dijkstrw/5x5/debug.c

/*
 * Debugging routines that help determine the nature of hard faults
 *
 * When linked in will override libopencm3's default hardfault handler.
 *
 * Original by Erich Styger via
 * http://mcuoneclipse.com/2012/11/24/debugging-hard-faults-on-arm-cortex-m/
 */

#include <libopencm3/cm3/scb.h>

void hardfault_discovery(struct scb_exception_stack_frame *frame);
void hardfault_discovery(struct scb_exception_stack_frame *frame)
{
    volatile uint32_t _CFSR;
    volatile uint32_t _HFSR;
    volatile uint32_t _DFSR;
    volatile uint32_t _AFSR;
    volatile uint32_t _BFAR;
    volatile uint32_t _MMAR;

    (void)(frame);
    /*
     * - Configurable Fault Status Register, MMSR, BFSR and UFSR
     * - Hard Fault Status Register
     * - Debug Fault Status Register
     * - Auxiliary Fault Status Register
     */
    _CFSR = SCB_CFSR;
    _HFSR = SCB_HFSR;
    _DFSR = SCB_DFSR;
    _AFSR = SCB_AFSR;

    /*
     * Fault address registers
     * - MemManage Fault Address Register
     * - Bus Fault Address Register
     */
    if (_CFSR & SCB_CFSR_MMARVALID)
        _MMAR = SCB_MMFAR;
    else
        _MMAR = 0;

    if (_CFSR & SCB_CFSR_BFARVALID)
        _BFAR = SCB_BFAR;
    else
        _BFAR = 0;

    (_CFSR);
    (_HFSR);
    (_DFSR);
    (_AFSR);
    (_BFAR);
    (_MMAR);

    __asm("BKPT #0\n") ; // Break into the debugger
}

__attribute__((naked)) void hardfault_handler(void);
__attribute__((naked)) void hardfault_handler(void)
{
  __asm volatile (
    "movs r0,#4            \n"
    "movs r1, lr           \n"
    "tst r0, r1            \n"
    "beq _MSP              \n"
    "mrs r0, psp           \n"
    "b _HALT               \n"
  "_MSP:                   \n"
    "mrs r0, msp           \n"
  "_HALT:                  \n"
    "ldr r1,[r0,#20]       \n"
    "b hardfault_discovery \n"
    "bkpt #0               \n"
  );
}

#pragma weak hard_fault_handler = hardfault_handler
